Nischalm1996/Paralysis_Assist/2.jpg

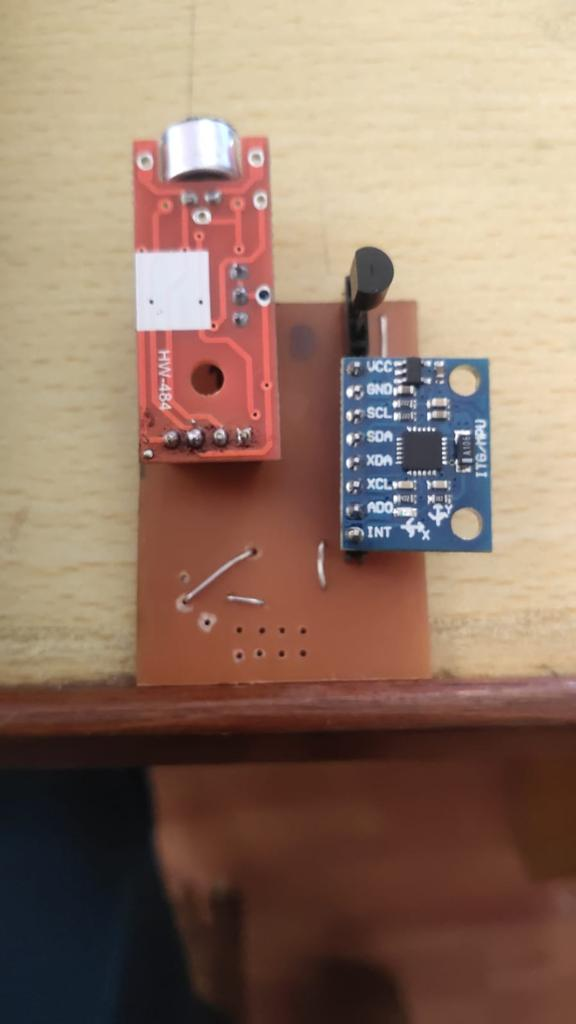
2.jpg
