Nischalm1996/Paralysis_Assist/3.jpg

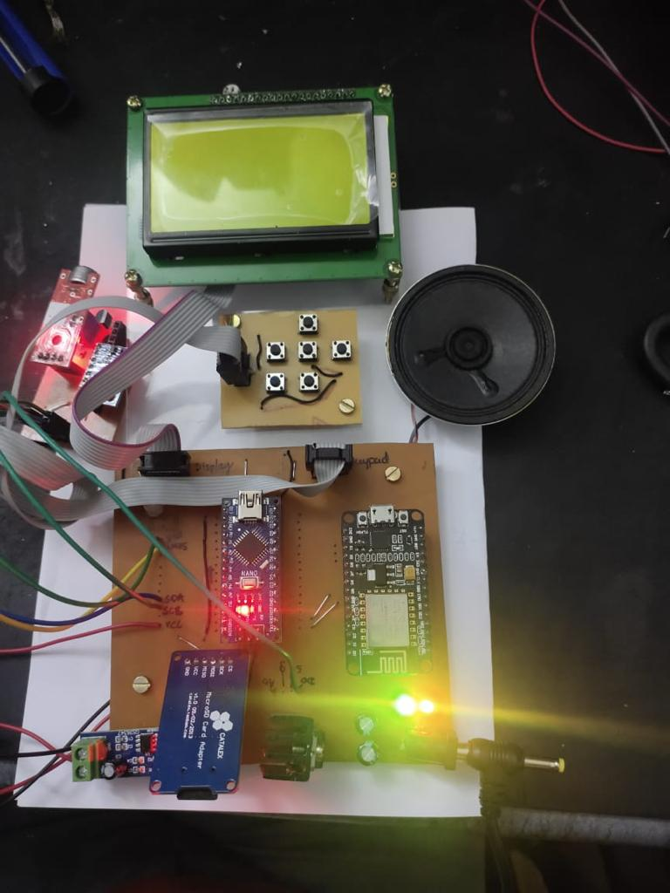
3.jpg
