Nischalm1996/Paralysis_Assist/4.jpg

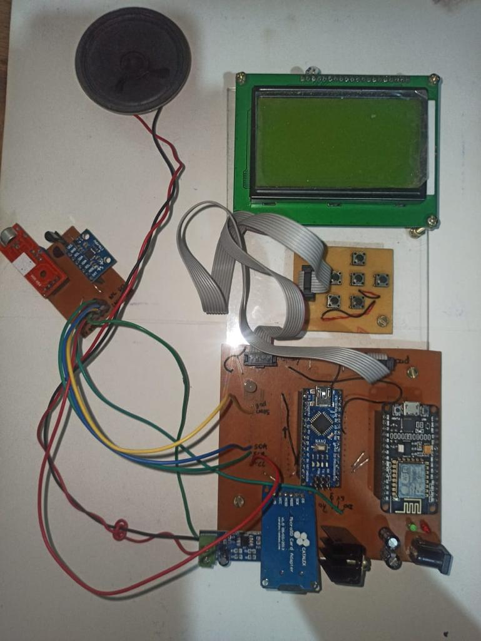
4.jpg
