Nischalm1996/Paralysis_Assist/6.jpg

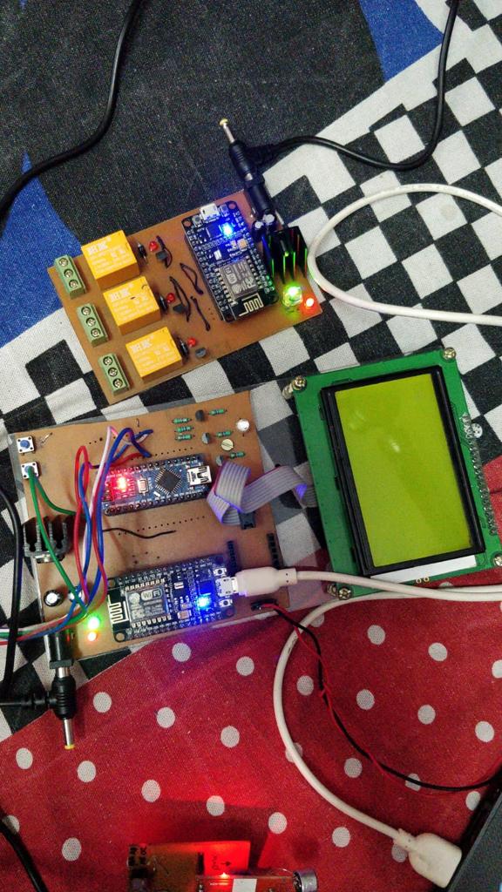
6.jpg
