Nischalm1996/Paralysis_Assist/penvmon/penvmon.sch

## EAGLE design penvmon/penvmon.sch (2021-03-12)

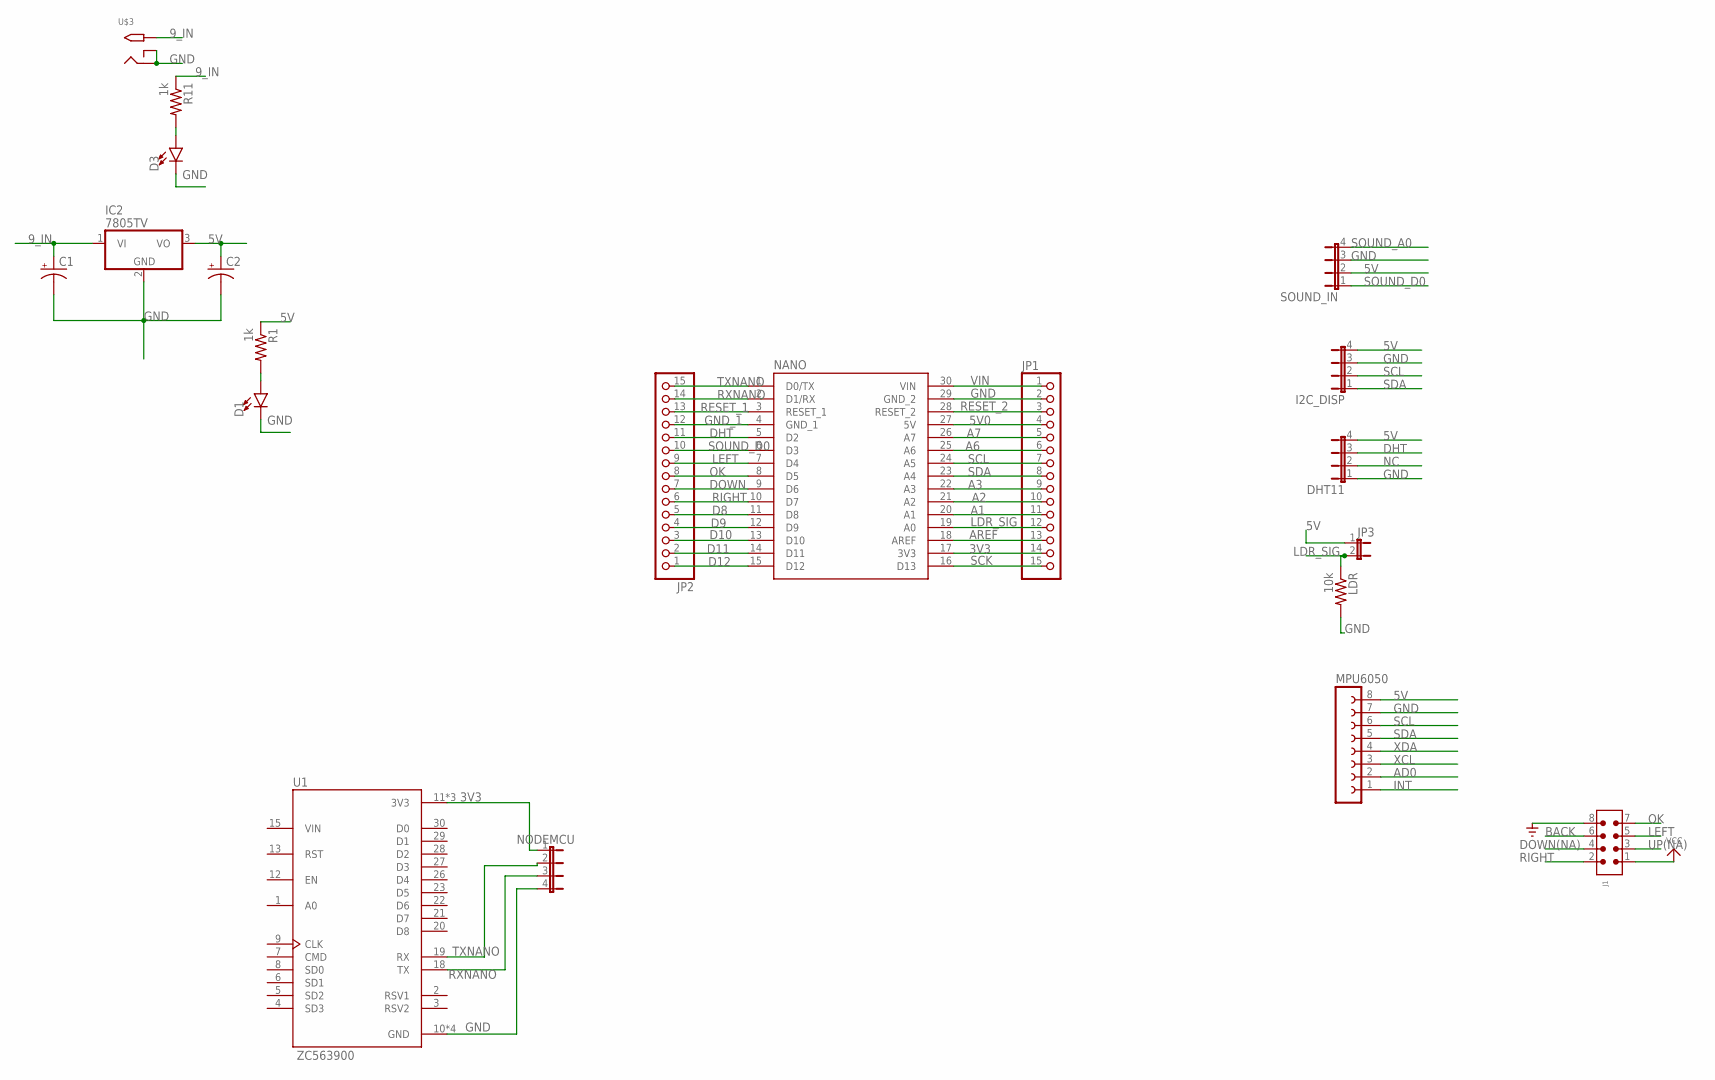
[picture p21: schematic penvmon.sch]

Parts:
C1, C2: CPOL-USE3.5-8; E3,5-8
D1, D3: LED3MM; LED_3MM
DHT11: JP4E; JP4
I2C_DISP: JP4E; JP4
IC2: 7805TV; TO220V
J1: 6120XX21621_61200821621; 61200821621
JP1, JP2: PINHD-1X15; 1X15
JP3: JP1E; JP1
LDR: 10k; M0805
MPU6050: FE08-1; FE08
NANO: A000005; MODULE_A000005
NODEMCU: JP4E; JP4
R1, R11: 1k; M0805
SOUND_IN: JP4E; JP4
U1: ZC563900; MODULE_ZC563900
U$3: 2.1MMJACKTHM; PJ-102A

Connections:
3V3: JP1.14, NANO.17 (3V3), NODEMCU.1, U1.11 (3V3)
5V: C2.+, DHT11.4, I2C_DISP.4, IC2.3 (VO), JP3.1, MPU6050.8, R1.1, SOUND_IN.2
5V0: JP1.4, NANO.27 (5V)
9_IN: C1.+, IC2.1 (VI), R11.1, U$3.TIP
A1: JP1.11, NANO.20 (A1)
A2: JP1.10, NANO.21 (A2)
A3: JP1.9, NANO.22 (A3)
A6: JP1.6, NANO.25 (A6)
A7: JP1.5, NANO.26 (A7)
AD0: MPU6050.2
AREF: JP1.13, NANO.18 (AREF)
BACK: J1.6
D8: JP2.5, NANO.11 (D8)
D9: JP2.4, NANO.12 (D9)
D10: JP2.3, NANO.13 (D10)
D11: JP2.2, NANO.14 (D11)
D12: JP2.1, NANO.15 (D12)
DHT: DHT11.3, JP2.11, NANO.5 (D2)
DOWN: JP2.7, NANO.9 (D6)
DOWN(NA): J1.4
GND: C1.-, C2.-, D1.K (C), D3.K (C), DHT11.1, I2C_DISP.3, IC2.2 (GND), J1.8, JP1.2, LDR.2, MPU6050.7, NANO.29 (GND_2), NODEMCU.4, SOUND_IN.3, U1.10 (GND), U$3.RING, U$3.RING_SW
GND_1: JP2.12, NANO.4 (GND_1)
INT: MPU6050.1
LDR_SIG: JP1.12, JP3.2, LDR.1, NANO.19 (A0)
LEFT: J1.5, JP2.9, NANO.7 (D4)
unnamed: D3.A, R11.2
unnamed: D1.A, R1.2
NC: DHT11.2
OK: J1.7, JP2.8, NANO.8 (D5)
RESET_1: JP2.13, NANO.3 (RESET_1)
RESET_2: JP1.3, NANO.28 (RESET_2)
RIGHT: J1.2, JP2.6, NANO.10 (D7)
RXNANO: JP2.14, NANO.2 (D1/RX), NODEMCU.3, U1.18 (TX)
SCK: JP1.15, NANO.16 (D13)
SCL: I2C_DISP.2, JP1.7, MPU6050.6, NANO.24 (A5)
SDA: I2C_DISP.1, JP1.8, MPU6050.5, NANO.23 (A4)
SOUND_A0: SOUND_IN.4
SOUND_D0: JP2.10, NANO.6 (D3), SOUND_IN.1
TXNANO: JP2.15, NANO.1 (D0/TX), NODEMCU.2, U1.19 (RX)
UP(NA): J1.3
VCC: J1.1
VIN: JP1.1, NANO.30 (VIN)
XCL: MPU6050.3
XDA: MPU6050.4
